shop2007/LegacyGuard-Wireless-Extender/foto prototipi/Master board 2.jpg

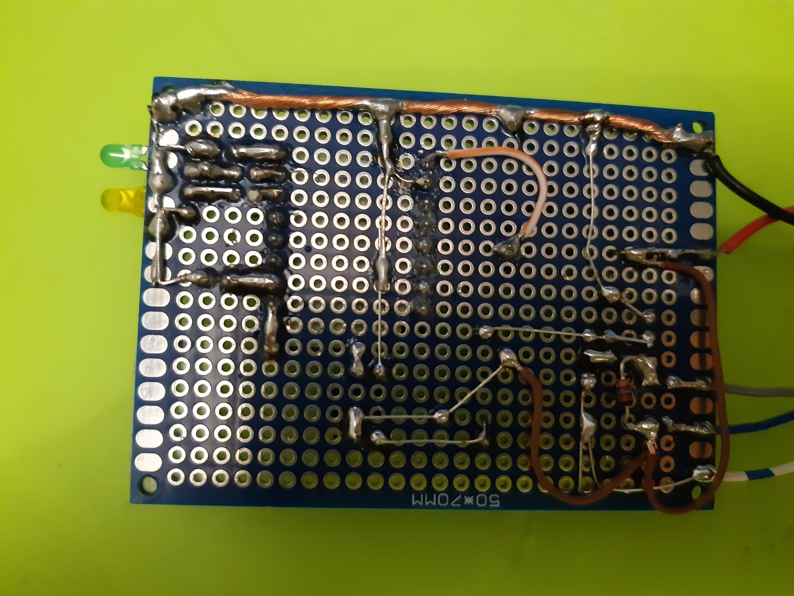
foto prototipi/Master board 2.jpg
