shop2007/LegacyGuard-Wireless-Extender/foto prototipi/Master con display acceso Slave 2 e 5 connessi.jpg

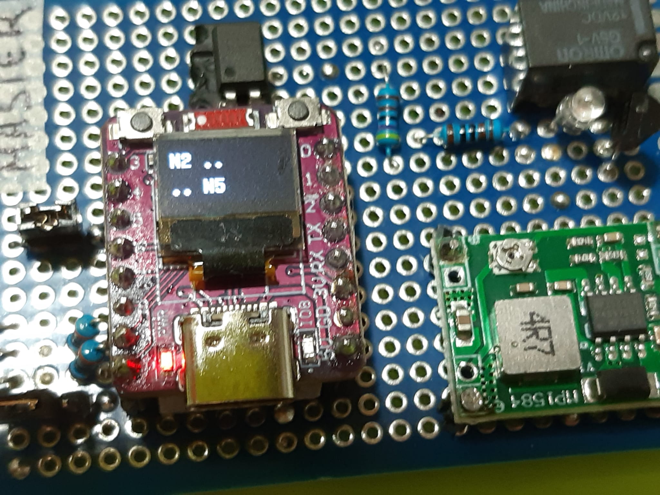
foto prototipi/Master con display acceso Slave 2 e 5 connessi.jpg
