shop2007/LegacyGuard-Wireless-Extender/foto prototipi/Slave board proto.jpg

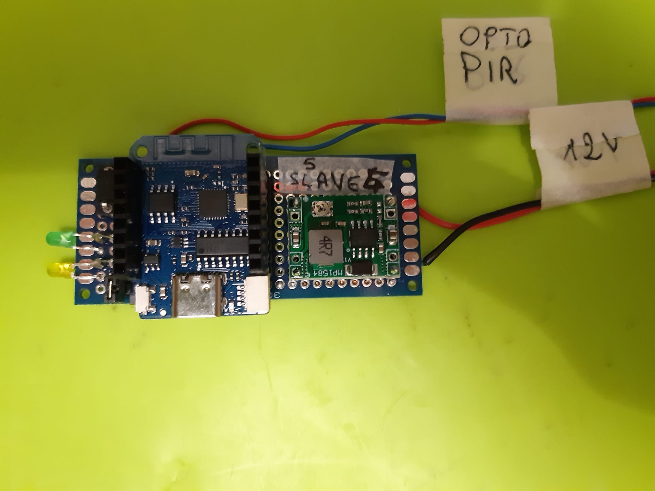
foto prototipi/Slave board proto.jpg
