shop2007/LegacyGuard-Wireless-Extender/master-board/hardware/Kicad/PIR_MASTER_ESP32C3DISPLAY047.kicad_sch

## KiCad design master-board/hardware/Kicad/PIR_MASTER_ESP32C3DISPLAY047.kicad_sch (2026-08-03)

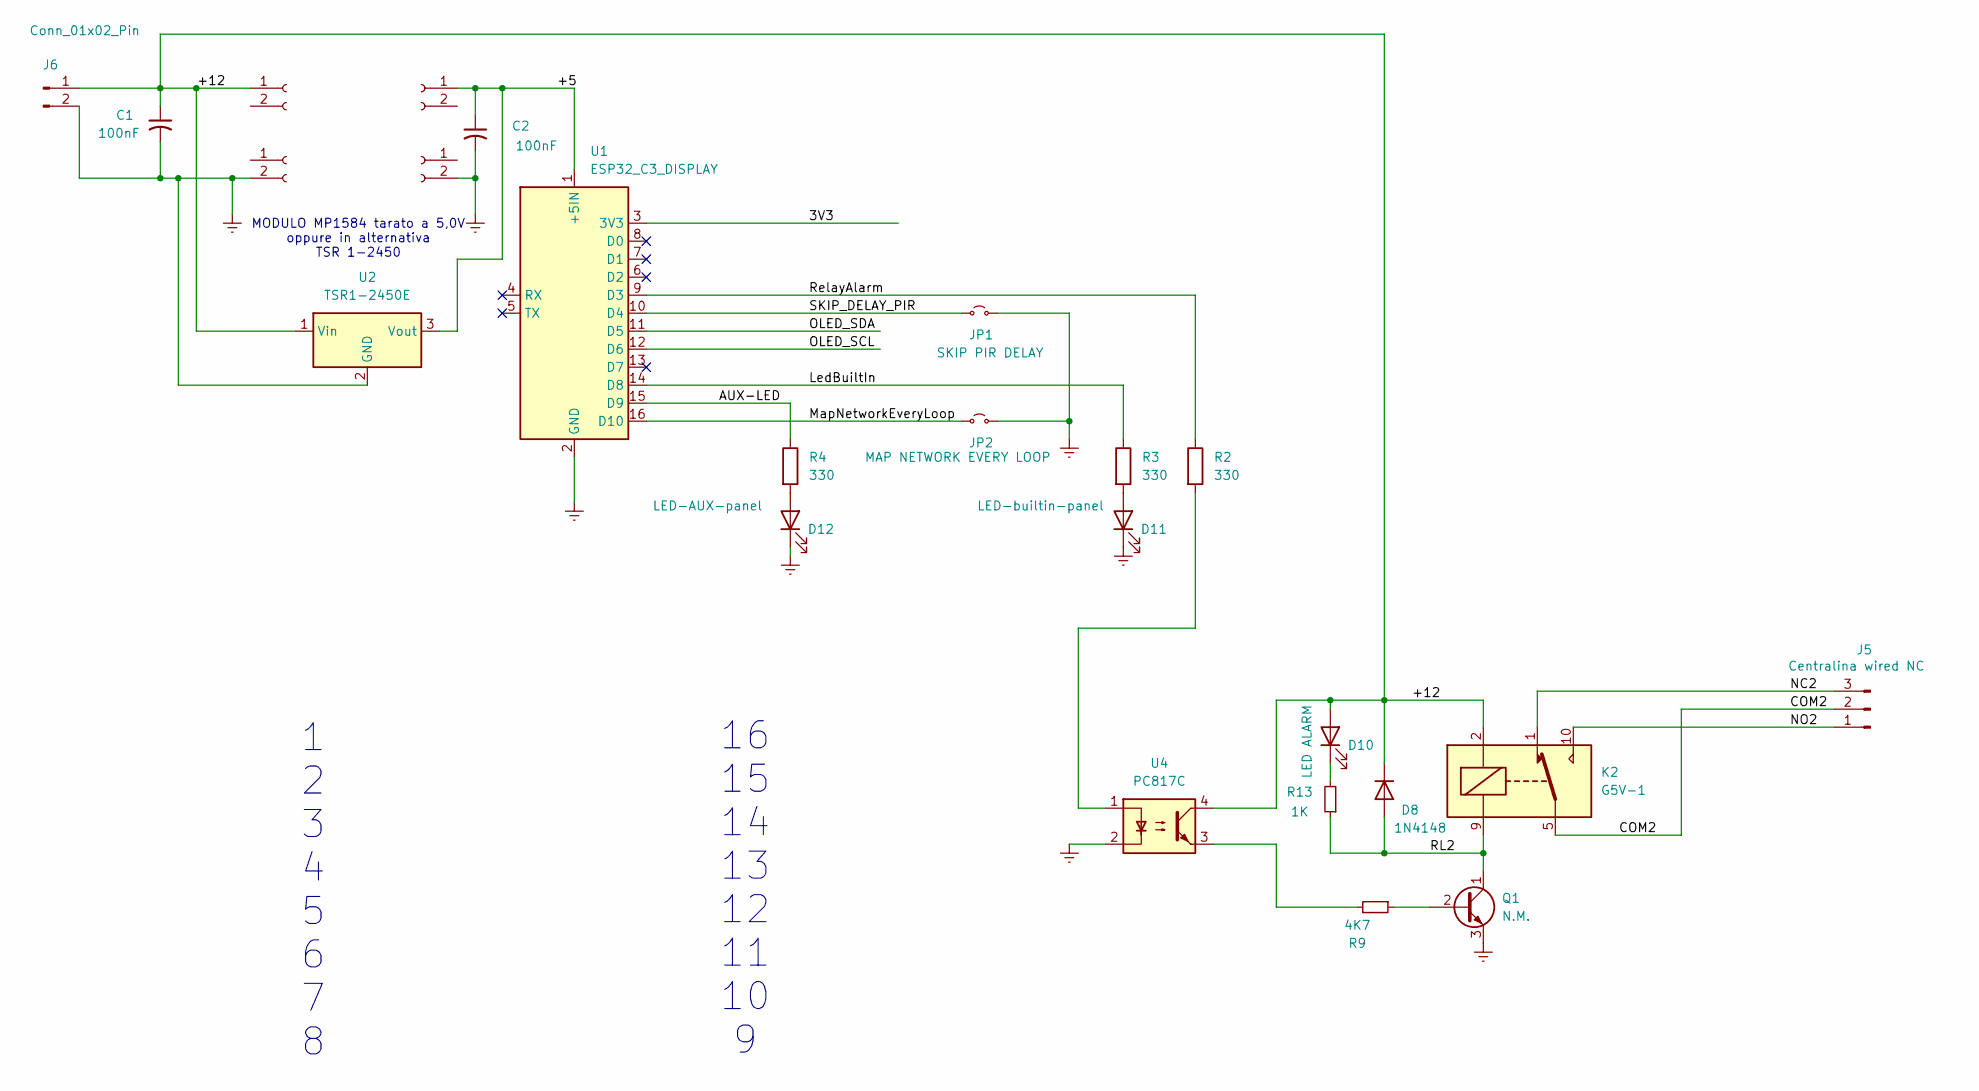
[picture p15: schematic PIR_MASTER_ESP32C3DISPLAY047.kicad_sch]

Parts:
C1, C2: 100nF
D8: 1N4148; D_DO-41_SOD81_P2.54mm_Vertical_AnodeUp
D10: LED ALARM; LED_D3.0mm
D11: LED-builtin-panel; LED_D3.0mm
D12: LED-AUX-panel; LED_D3.0mm
J1, J2, J3, J4: Conn_01x02_Socket
J5: Centralina wired NC; Wago_734-133_1x03_P3.50mm_Vertical
J6: Conn_01x02_Pin
JP1: SKIP PIR DELAY
JP2: MAP NETWORK EVERY LOOP
K2: G5V-1; Relay_SPDT_Omron_G5V-1
Q1: N.M.; TO-92_HandSolder
R2, R3, R4: 330
R9: 4K7; R_Axial_DIN0204_L3.6mm_D1.6mm_P2.54mm_Vertical
R13: 1K; R_Axial_DIN0204_L3.6mm_D1.6mm_P2.54mm_Vertical
U1: ESP32_C3_DISPLAY; WEMOS_C3_mini
U2: TSR1-2450E; Converter_DCDC_TRACO_TSR1-xxxxE_THT
U4: PC817C; DIP-4_W7.62mm

Connections:
3V3: U1.3 (3V3)
+5: C2.1, J3.1, U1.1 (+5IN), U2.3 (Vout)
+12: C1.1, D8.1 (K), D10.2 (A), J1.1, J6.1, K2.2, U2.1 (Vin), U4.4
AUX-LED: R4.1, U1.15 (D9)
COM2: J5.2, K2.5, K2.6
GNDREF: C1.2, C2.2, D11.1 (K), D12.1 (K), J2.2, J4.2, J6.2, JP1.2 (B), JP2.2 (B), Q1.3 (E), U1.2 (GND), U2.2 (GND), U4.2
LedBuiltIn: R3.1, U1.14 (D8)
MapNetworkEveryLoop: JP2.1 (A), U1.16 (D10)
NC2: J5.3, K2.1
NO2: J5.1, K2.10
unnamed: D10.1 (K), R13.2
unnamed: D11.2 (A), R3.2
unnamed: D12.2 (A), R4.2
unnamed: Q1.2 (B), R9.1
unnamed: R2.2, U4.1
unnamed: R9.2, U4.3
OLED_SCL: U1.12 (D6)
OLED_SDA: U1.11 (D5)
RL2: D8.2 (A), K2.9, Q1.1 (C), R13.1
RelayAlarm: R2.1, U1.9 (D3)
SKIP_DELAY_PIR: JP1.1 (A), U1.10 (D4)

Notes on the sheet:
1 2 3 4 5 6 7 8
16 15 14 13 12 11 10 9
MODULO MP1584 tarato a 5,0V oppure in alternativa TSR 1-2450
