shop2007/LegacyGuard-Wireless-Extender/slave-board/hardware/Kicad/PIR_SLAVE_8266.kicad_sch

## KiCad design slave-board/hardware/Kicad/PIR_SLAVE_8266.kicad_sch (2026-08-03)

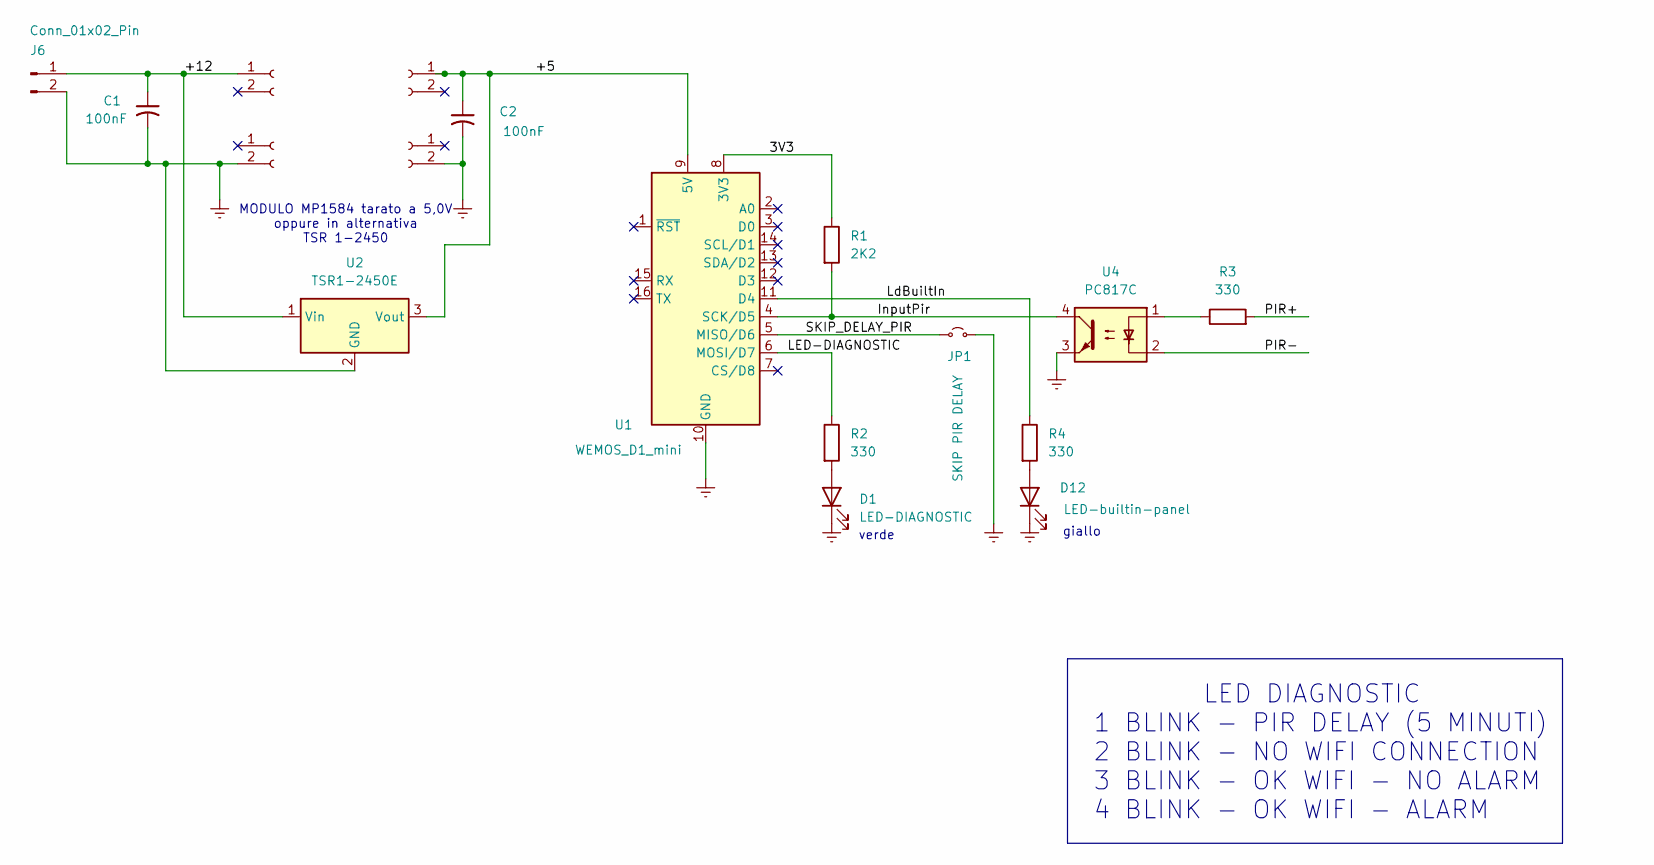
[picture p16: schematic PIR_SLAVE_8266.kicad_sch]

Parts:
C1, C2: 100nF
D1: LED-DIAGNOSTIC
D12: LED-builtin-panel; LED_D3.0mm
J1, J2, J3, J4: Conn_01x02_Socket
J6: Conn_01x02_Pin
JP1: SKIP PIR DELAY
R1: 2K2
R2, R3, R4: 330
U1: WEMOS_D1_mini; WEMOS_D1_mini_light
U2: TSR1-2450E; Converter_DCDC_TRACO_TSR1-xxxxE_THT
U4: PC817C; DIP-4_W7.62mm

Connections:
3V3: R1.1, U1.8 (3V3)
+5: C2.1, J3.1, U1.9 (5V), U2.3 (Vout)
+12: C1.1, J1.1, J6.1, U2.1 (Vin)
GNDREF: C1.2, C2.2, D1.1 (K), D12.1 (K), J2.2, J4.2, J6.2, JP1.2 (B), U1.10 (GND), U2.2 (GND), U4.3
InputPir: R1.2, U1.4 (SCK/D5), U4.4
LED-DIAGNOSTIC: R2.1, U1.6 (MOSI/D7)
LdBuiltIn: R4.1, U1.11 (D4)
unnamed: D1.2 (A), R2.2
unnamed: D12.2 (A), R4.2
unnamed: R3.1, U4.1
PIR+: R3.2
PIR-: U4.2
SKIP_DELAY_PIR: JP1.1 (A), U1.5 (MISO/D6)

Notes on the sheet:
giallo
LED DIAGNOSTIC 1 BLINK - PIR DELAY (5 MINUTI) 2 BLINK - NO WIFI CONNECTION 3 BLINK - OK WIFI - NO ALARM 4 BLINK - OK WIFI - ALARM
MODULO MP1584 tarato a 5,0V oppure in alternativa TSR 1-2450
verde
